xdylanm/gate-delay/docs/assets/images/gate-delay-1.jpg

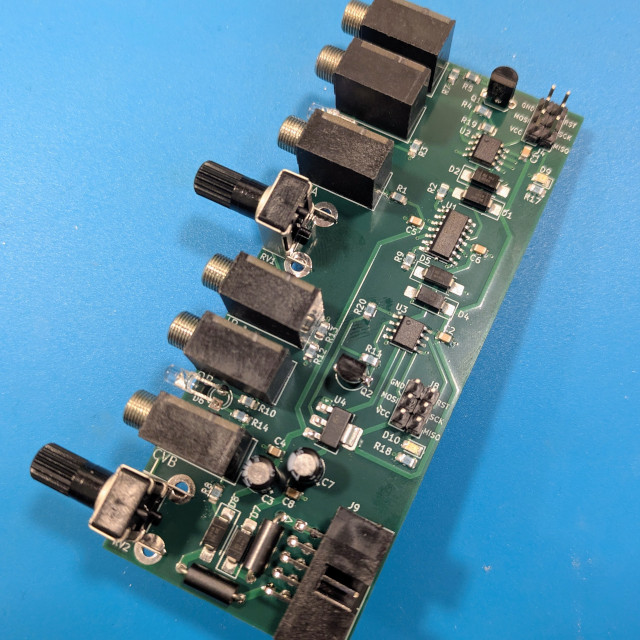
docs/assets/images/gate-delay-1.jpg
